Panomicron/Chromium/Chromium/Hardware/Body/bottom housing & cover 1-2/new/bottom housing - new.3mf

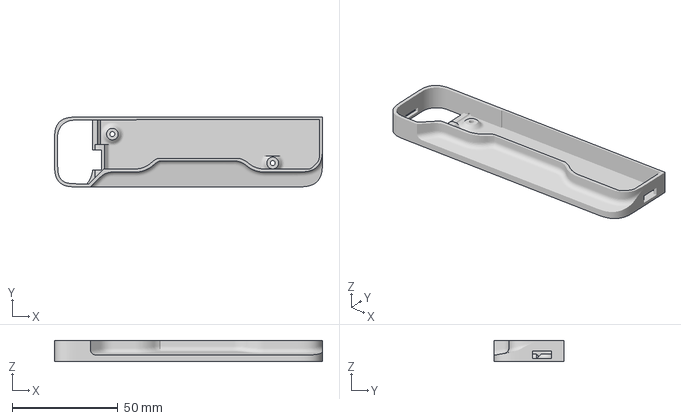
[picture p15: CAD file, 2021-07-30]
Chromium/Hardware/Body/bottom housing & cover 1-2/new/bottom housing - new.3mf
126.5 x 33.0 x 10.0 mm
