Panomicron/Chromium/Chromium/Hardware/Body/film door latch - lock.3mf

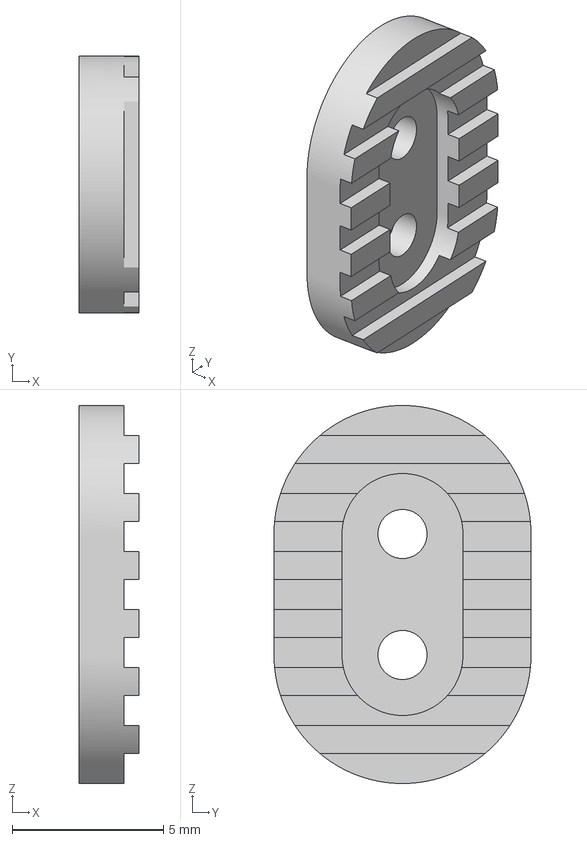
[picture p16: CAD file, 2021-07-30]
Chromium/Hardware/Body/film door latch - lock.3mf
2.00 x 8.50 x 12.5 mm
