Panomicron/Chromium/Chromium/Hardware/Body/geartrain/10 teeth.3mf

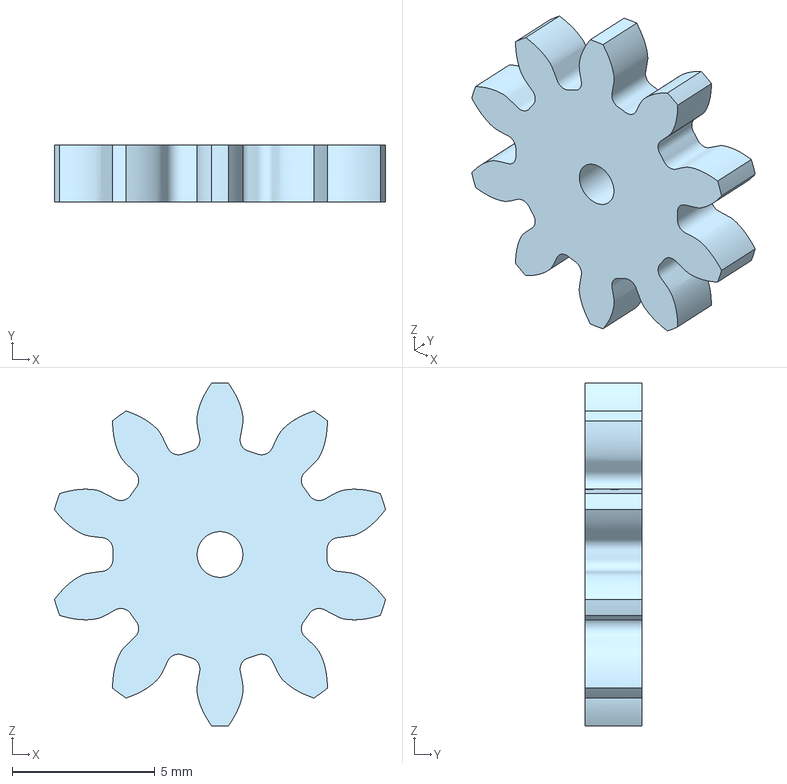
[picture p17: CAD file, 2021-07-30]
Chromium/Hardware/Body/geartrain/10 teeth.3mf
11.6 x 2.00 x 12.0 mm
