Panomicron/Chromium/Chromium/Hardware/Body/bottom housing & cover 1-2/new/battery door latch.3mf

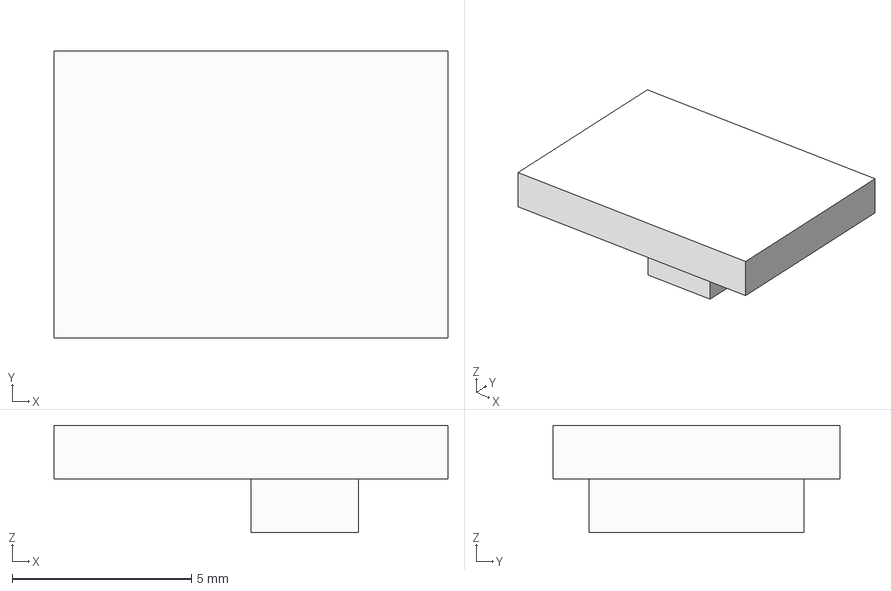
[picture p18: CAD file, 2021-07-30]
Chromium/Hardware/Body/bottom housing & cover 1-2/new/battery door latch.3mf
11.0 x 8.00 x 3.00 mm
