Panomicron/Chromium/Chromium/Hardware/Body/film door latch - baselpate.3mf

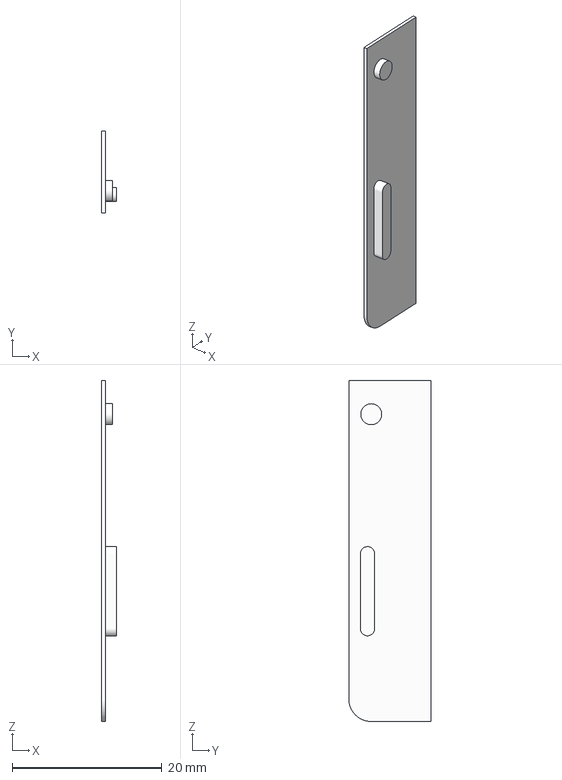
[picture p19: CAD file, 2021-07-30]
Chromium/Hardware/Body/film door latch - baselpate.3mf
2.00 x 11.0 x 45.5 mm
