Panomicron/Chromium/Chromium/Hardware/Body/geartrain/Canister gear -16 teeth.3mf

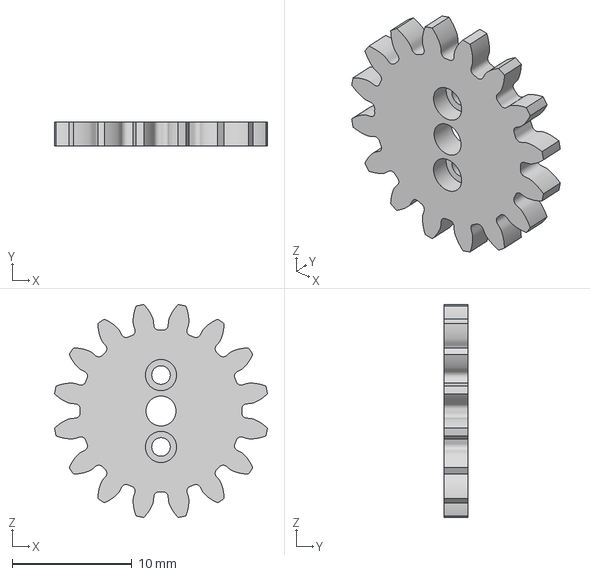
[picture p20: CAD file, 2021-07-30]
Chromium/Hardware/Body/geartrain/Canister gear -16 teeth.3mf
17.8 x 2.00 x 17.8 mm
