Panomicron/Chromium/Chromium/Hardware/Body/film gate.3mf

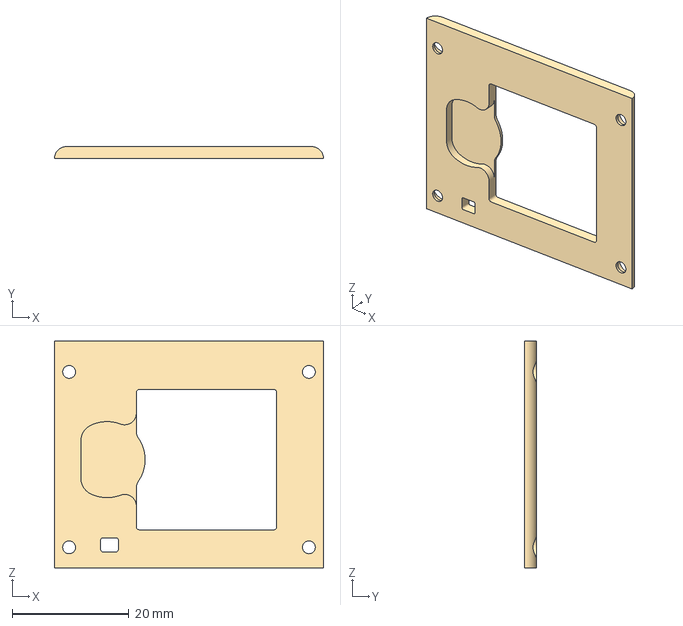
[picture p21: CAD file, 2021-07-30]
Chromium/Hardware/Body/film gate.3mf
46.0 x 2.00 x 38.8 mm
