Panomicron/Chromium/Chromium/Hardware/Body/geartrain/12 teeth.3mf

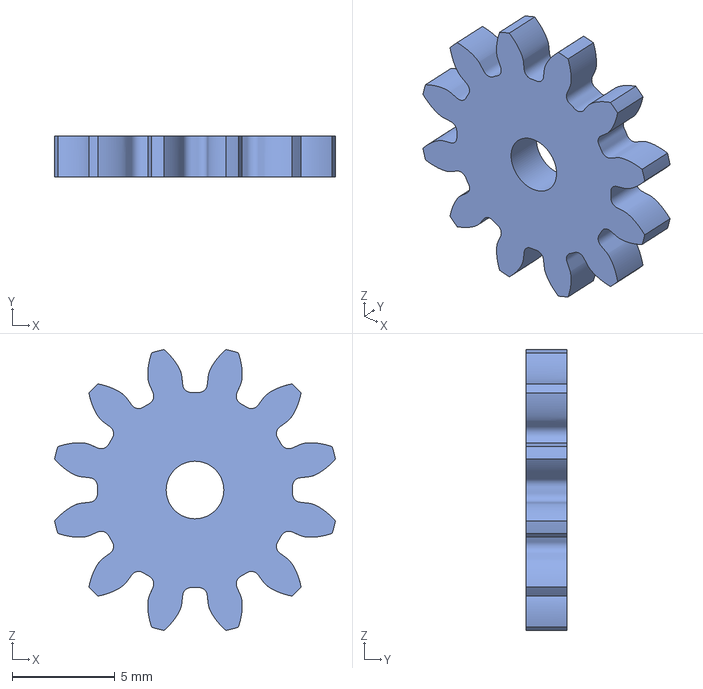
[picture p22: CAD file, 2021-07-30]
Chromium/Hardware/Body/geartrain/12 teeth.3mf
13.7 x 2.00 x 13.7 mm
