Panomicron/Chromium/Chromium/Hardware/Body/5. top housing spacer.3mf

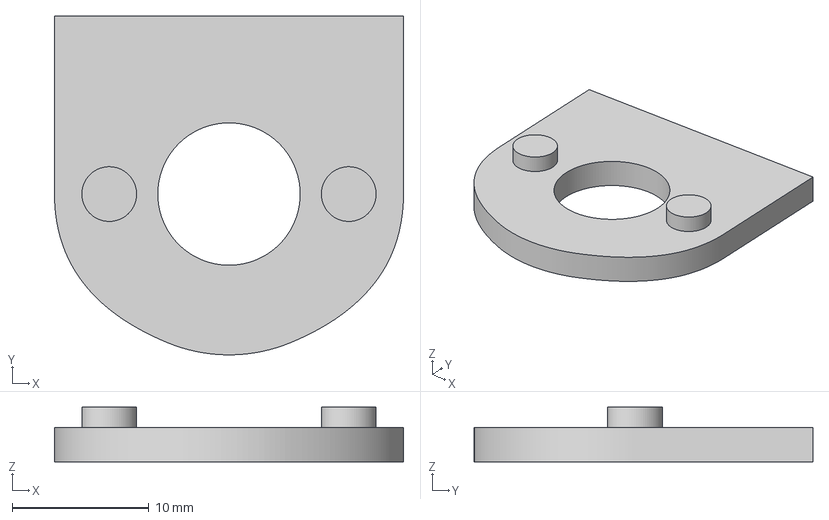
[picture p23: CAD file, 2021-07-30]
Chromium/Hardware/Body/5. top housing spacer.3mf
25.5 x 24.7 x 4.00 mm
