Panomicron/Chromium/Chromium/Hardware/Body/geartrain/film takeup.3mf

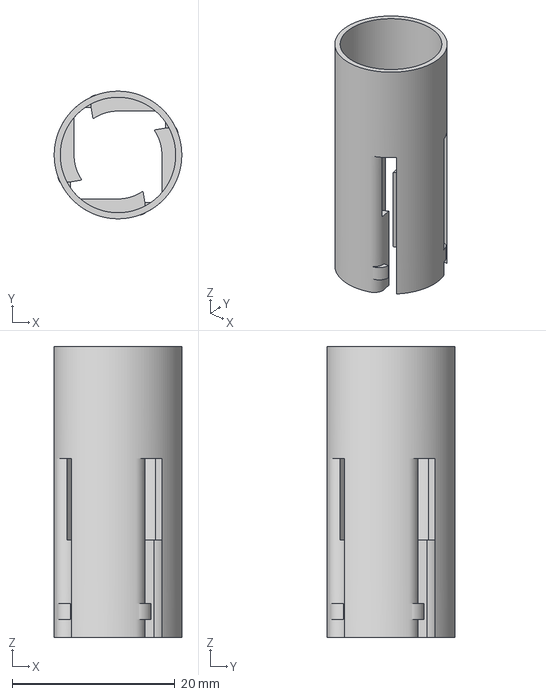
[picture p24: CAD file, 2021-07-30]
Chromium/Hardware/Body/geartrain/film takeup.3mf
15.7 x 15.7 x 35.8 mm
