Panomicron/Chromium/Chromium/Hardware/Body/6.top plate.3mf

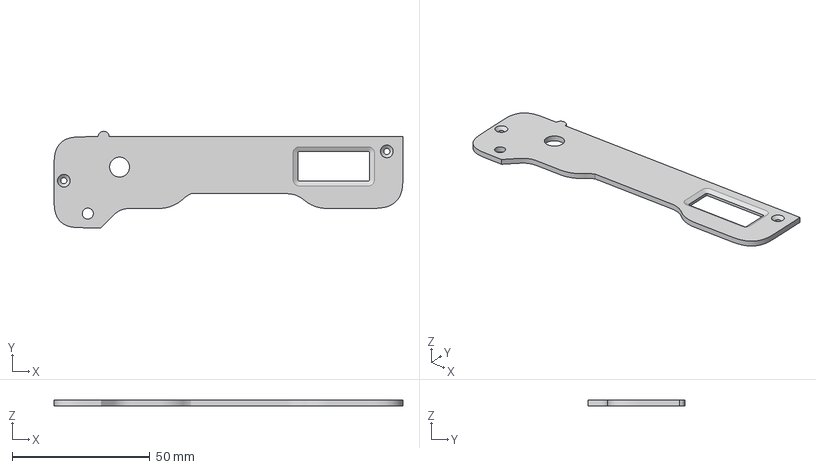
[picture p25: CAD file, 2021-07-30]
Chromium/Hardware/Body/6.top plate.3mf
126.5 x 35.0 x 2.00 mm
