Panomicron/Chromium/Chromium/Hardware/Body/geartrain/geartrain baseplate.3mf

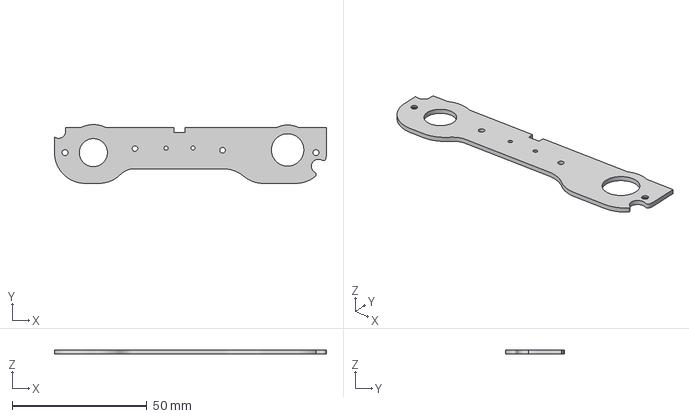
[picture p26: CAD file, 2021-07-30]
Chromium/Hardware/Body/geartrain/geartrain baseplate.3mf
100.8 x 21.8 x 1.50 mm
