Panomicron/Chromium/Chromium/Hardware/Body/5. top housing.3mf

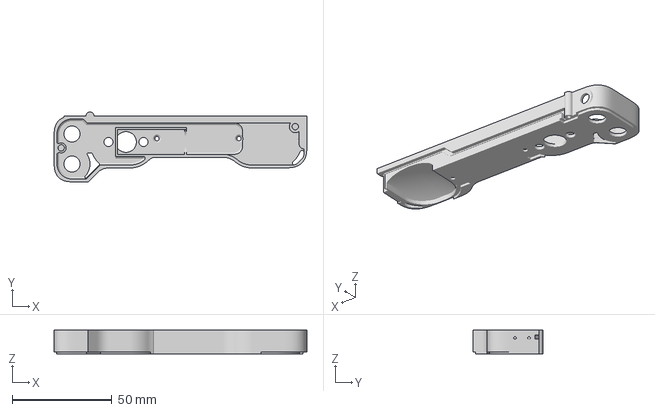
[picture p27: CAD file, 2021-07-30]
Chromium/Hardware/Body/5. top housing.3mf
126.5 x 35.0 x 12.0 mm
