Panomicron/Chromium/Chromium/Hardware/Body/geartrain/13 teeth.3mf

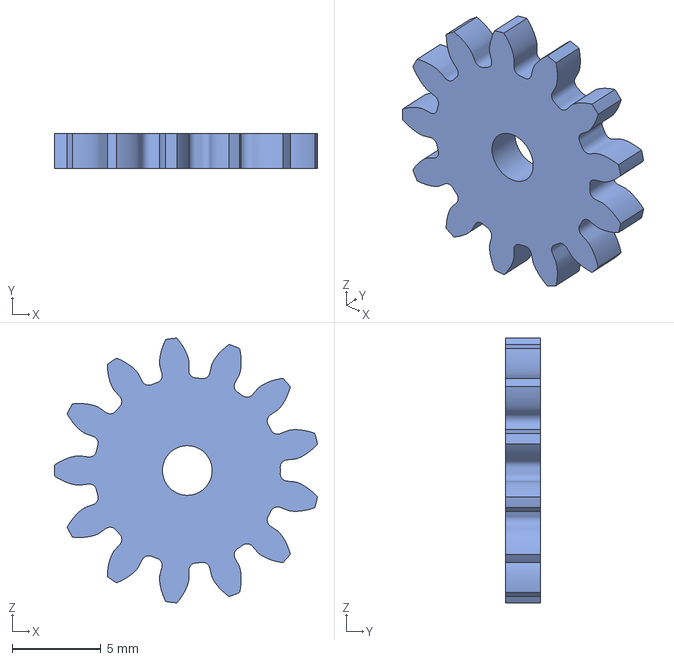
[picture p28: CAD file, 2021-07-30]
Chromium/Hardware/Body/geartrain/13 teeth.3mf
14.9 x 2.00 x 15.0 mm
