Panomicron/Chromium/Chromium/Hardware/Body/0.03inch spacer.3mf

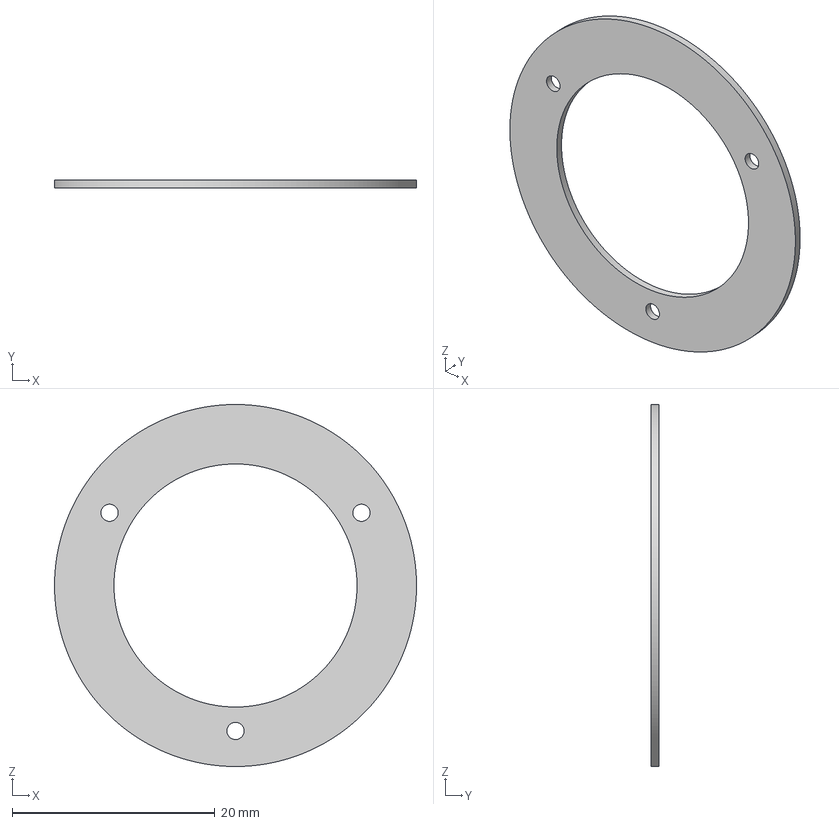
[picture p29: CAD file, 2021-07-30]
Chromium/Hardware/Body/0.03inch spacer.3mf
35.7 x 0.762 x 35.7 mm
