Panomicron/Chromium/Chromium/Hardware/Body/geartrain/18 teeth.3mf

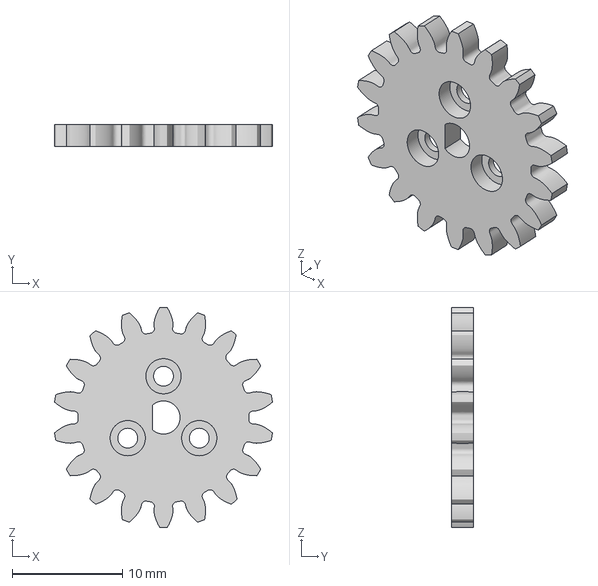
[picture p30: CAD file, 2021-07-30]
Chromium/Hardware/Body/geartrain/18 teeth.3mf
19.8 x 2.00 x 20.0 mm
