Panomicron/Chromium/Chromium/Hardware/Body/4 body.3mf

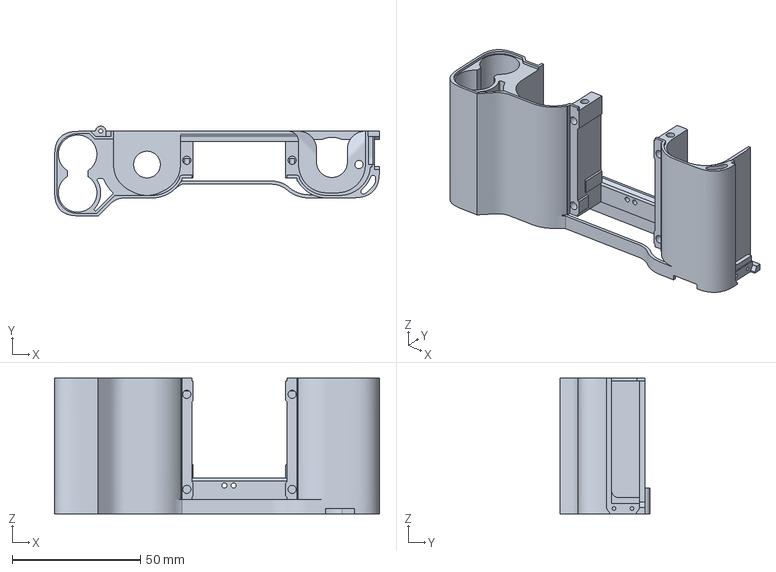
[picture p31: CAD file, 2021-07-30]
Chromium/Hardware/Body/4 body.3mf
126.5 x 35.0 x 52.8 mm
