Panomicron/Chromium/Chromium/Hardware/Body/geartrain/Canister pickup - 16 teeth.3mf

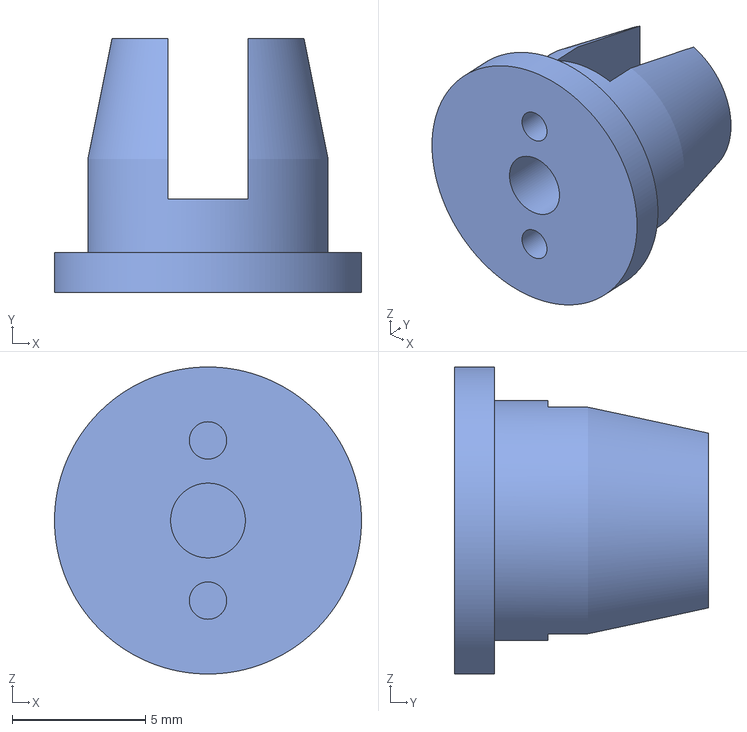
[picture p32: CAD file, 2021-07-30]
Chromium/Hardware/Body/geartrain/Canister pickup - 16 teeth.3mf
11.5 x 9.50 x 11.5 mm
