Panomicron/Chromium/Chromium/Hardware/Body/battery contact cover.3mf

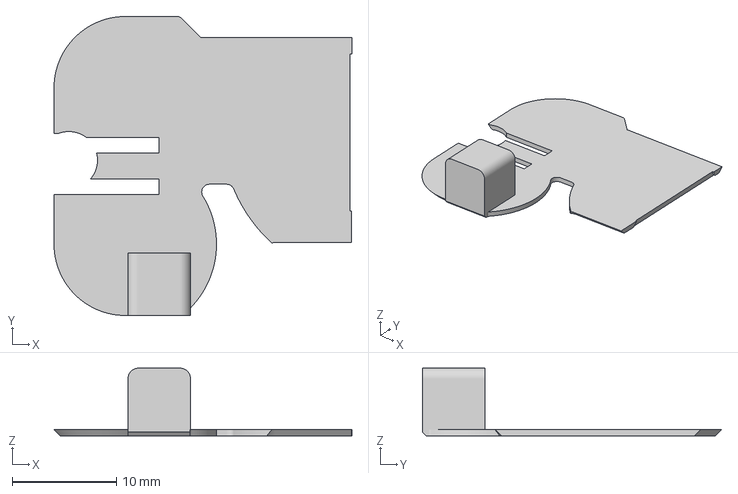
[picture p33: CAD file, 2021-07-30]
Chromium/Hardware/Body/battery contact cover.3mf
28.6 x 28.7 x 6.50 mm
