Panomicron/Chromium/Chromium/Hardware/Body/film door latch - cover.3mf

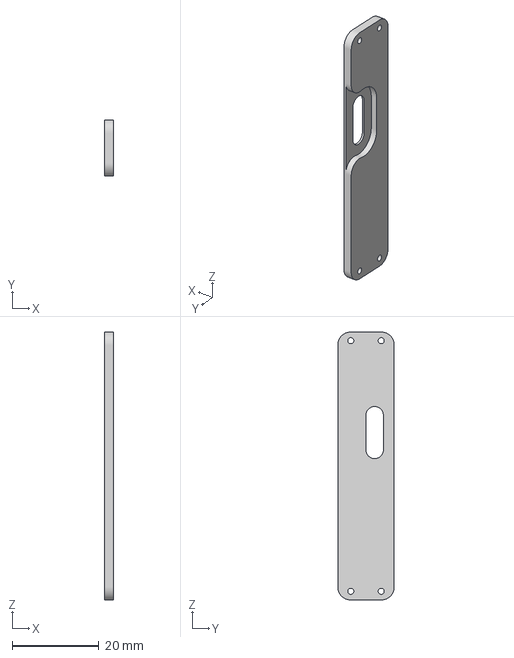
[picture p34: CAD file, 2021-07-30]
Chromium/Hardware/Body/film door latch - cover.3mf
2.00 x 13.0 x 61.7 mm
