Panomicron/Chromium/Chromium/Hardware/Body/shutter cover.3mf

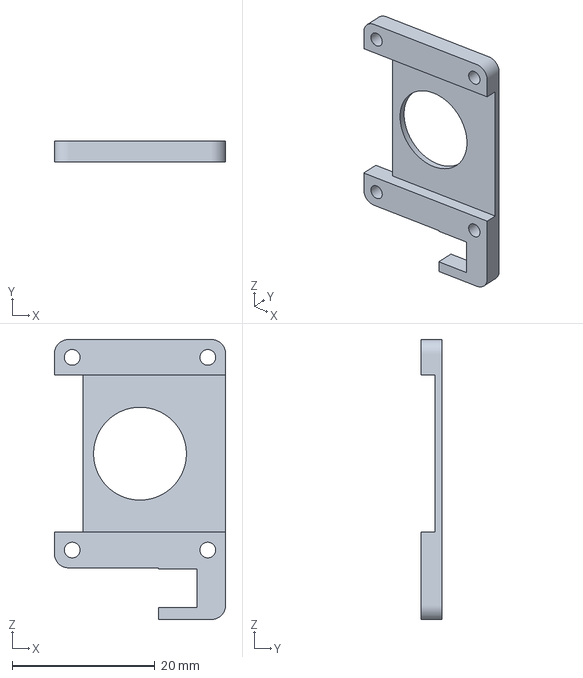
[picture p35: CAD file, 2021-07-30]
Chromium/Hardware/Body/shutter cover.3mf
24.0 x 3.00 x 39.2 mm
