Panomicron/Chromium/Chromium/Hardware/Body/Interface Holder.3mf

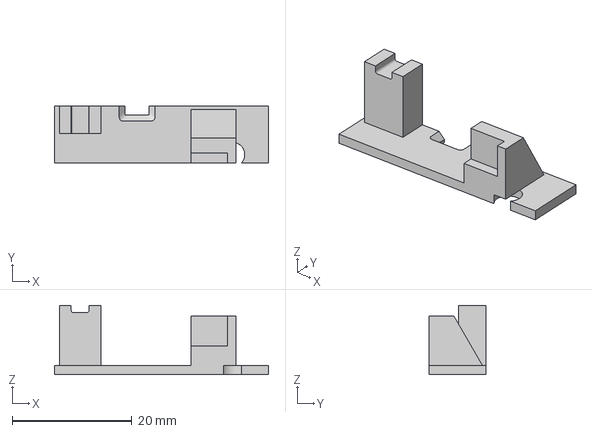
[picture p36: CAD file, 2021-07-30]
Chromium/Hardware/Body/Interface Holder.3mf
35.8 x 9.50 x 11.6 mm
